Roland-Scholz/Sally-2/pictures/sally-2-abbuc-b.jpg

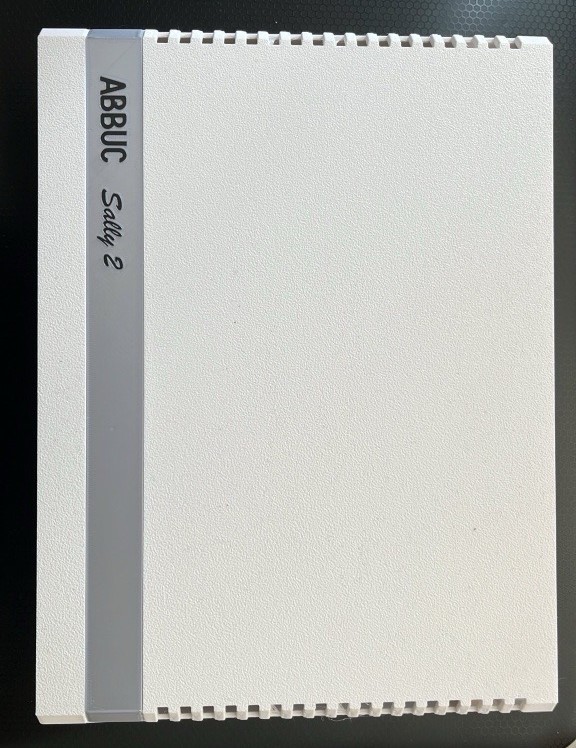
pictures/sally-2-abbuc-b.jpg
