Roland-Scholz/Sally-2/release/case/spacer-led.stl

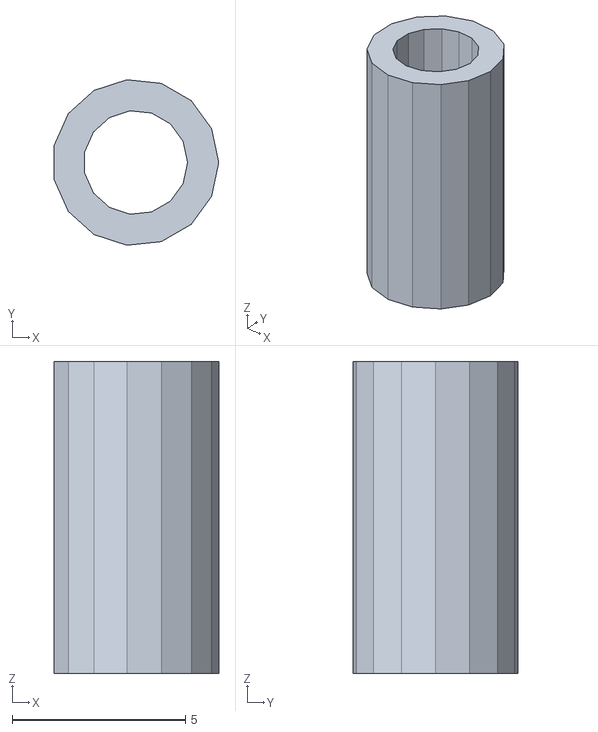
[picture p33: CAD file, 2025-09-01]
release/case/spacer-led.stl
4.75 x 4.77 x 9.00
