Roland-Scholz/Sally-2/case/sally-2-top-1a.stl

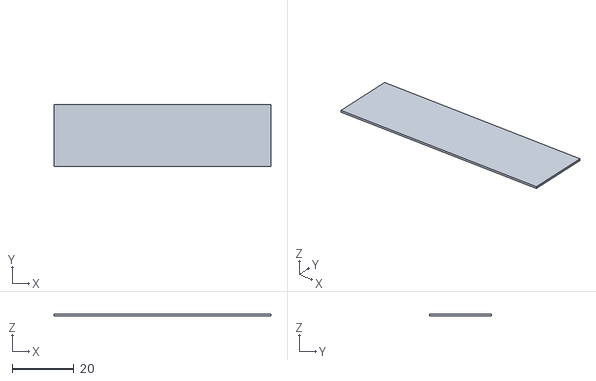
[picture p34: CAD file, 2025-05-10]
case/sally-2-top-1a.stl
70.0 x 20.0 x 0.6
