Roland-Scholz/Sally-2/release/case/sally-parts.3mf

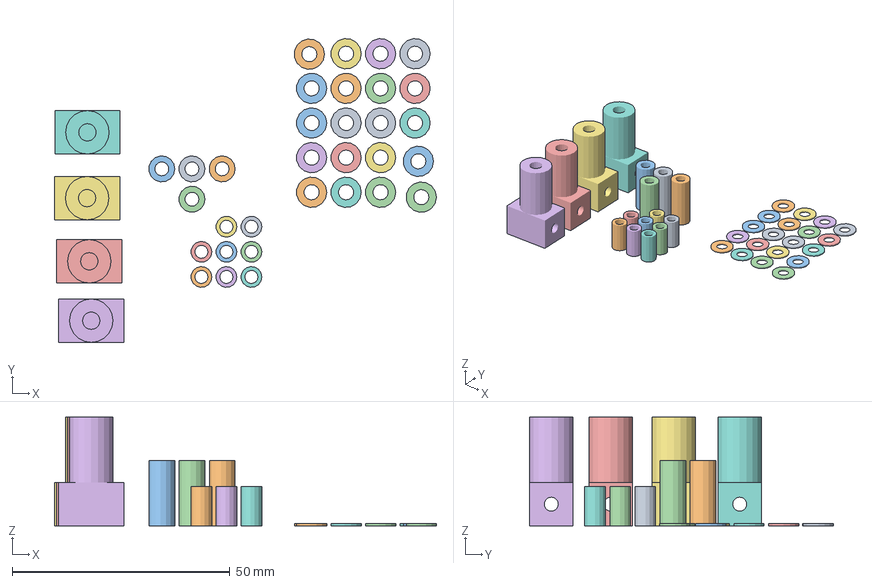
[picture p35: CAD file, 2025-09-01]
release/case/sally-parts.3mf
87.8 x 69.8 x 25.0 mm
spacer-round.stl x 4
washer.stl x 20
spacer.stl x 4
spacer-led.stl x 8
