Roland-Scholz/Sally-2/release/case/spacer.stl

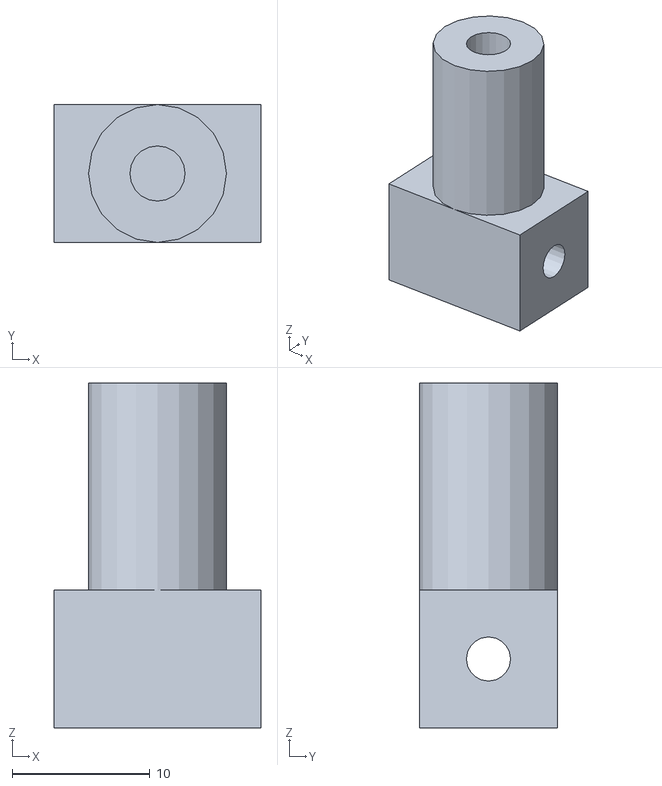
[picture p36: CAD file, 2025-09-01]
release/case/spacer.stl
15.0 x 10.0 x 25.0
