Roland-Scholz/Sally-2/case/spacer-led.scad

$fn = 15;

spacer_led();


module spacer_led() {
    difference(){
        cylinder(h=9, r=2.4);
            cylinder(h=9, r=1.5);
        
    };
}
