Roland-Scholz/Sally-2/case/spacer-round-15.scad

$fn = 15;

spacer_round_15();


module spacer_round_15() {
    difference(){
        cylinder(h=15, r=3);
            cylinder(h=15, r=1.6);
        
    };
}
