Roland-Scholz/Sally-2/case/spacer-round-9.scad

$fn = 15;

spacer_round_9();


module spacer_round_9() {
    difference(){
        cylinder(h=9, r=3);
            cylinder(h=9, r=1.6);
        
    };
}
