Roland-Scholz/Sally-2/LTspice/serout.asc

Q1: npn; BC547B
Q2: npn; BC547B
R1: res; 100000
R2: res; 1000
R3: res; 22000
R4: res; 47000
V1: voltage; EXP(0 5 0 0.000001 0.000052 0.0000001)
V2: voltage; 5
Named nets: output, 0, serin
.tran 0 0.0001 0
