Roland-Scholz/Sally-2/src/ddsysgen.asm

; Disassembly of the file "C:\github\Sally-1\ATR8000-CPM\ddsysgen.com"
; 
; CPU Type: Z80
; 
; Created with dZ80 2.0
; 
; on Monday, 26 of August 2024 at 07:51 PM
; 
0000 c30401    jp      0104h
0003 d431c1    call    nc,0c131h
0006 0d        dec     c
0007 2a0600    ld      hl,(0006h)
000a 01e0be    ld      bc,0bee0h
000d b7        or      a
000e ed42      sbc     hl,bc
0010 da0000    jp      c,0000h
0013 cd560a    call    0a56h
0016 0d        dec     c
0017 0a        ld      a,(bc)
0018 0a        ld      a,(bc)
0019 41        ld      b,c
001a 54        ld      d,h
001b 52        ld      d,d
001c 3830      jr      c,004eh          ; (+30h)
001e 3030      jr      nc,0050h         ; (+30h)
0020 2053      jr      nz,0075h         ; (+53h)
0022 79        ld      a,c
0023 73        ld      (hl),e
0024 74        ld      (hl),h
0025 65        ld      h,l
0026 6d        ld      l,l
0027 2047      jr      nz,0070h         ; (+47h)
0029 65        ld      h,l
002a 6e        ld      l,(hl)
002b 65        ld      h,l
002c 72        ld      (hl),d
002d 61        ld      h,c
002e 74        ld      (hl),h
002f 6f        ld      l,a
0030 72        ld      (hl),d
0031 2076      jr      nz,00a9h         ; (+76h)
0033 65        ld      h,l
0034 72        ld      (hl),d
0035 73        ld      (hl),e
0036 2032      jr      nz,006ah         ; (+32h)
0038 2e31      ld      l,31h
003a 0d        dec     c
003b 0a        ld      a,(bc)
003c 2d        dec     l
003d 2d        dec     l
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
00f4 69        ld      l,c
00f5 73        ld      (hl),e
00f6 6b        ld      l,e
00f7 2074      jr      nz,016dh         ; (+74h)
00f9 68        ld      l,b
00fa 61        ld      h,c
00fb 74        ld      (hl),h
00fc 2079      jr      nz,0177h         ; (+79h)
00fe 6f        ld      l,a
00ff 75        ld      (hl),l
0100 2077      jr      nz,0179h         ; (+77h)
0102 69        ld      l,c
0103 73        ld      (hl),e
0104 68        ld      l,b
0105 0d        dec     c
0106 0a        ld      a,(bc)
0107 74        ld      (hl),h
0108 6f        ld      l,a
0109 2077      jr      nz,0182h         ; (+77h)
010b 72        ld      (hl),d
010c 69        ld      l,c
010d 74        ld      (hl),h
010e 65        ld      h,l
010f 2043      jr      nz,0154h         ; (+43h)
0111 50        ld      d,b
0112 2f        cpl     
0113 4d        ld      c,l
0114 206f      jr      nz,0185h         ; (+6fh)
0116 6e        ld      l,(hl)
0117 74        ld      (hl),h
0118 6f        ld      l,a
0119 2069      jr      nz,0184h         ; (+69h)
011b 6e        ld      l,(hl)
011c 2064      jr      nz,0182h         ; (+64h)
011e 72        ld      (hl),d
011f 69        ld      l,c
0120 76        halt    
0121 65        ld      h,l
0122 2041      jr      nz,0165h         ; (+41h)
0124 3a2061    ld      a,(6120h)
0127 6e        ld      l,(hl)
0128 64        ld      h,h
0129 0d        dec     c
012a 0a        ld      a,(bc)
012b 00        nop     
012c af        xor     a
012d 323f0d    ld      (0d3fh),a
0130 3e02      ld      a,02h
0132 cd180b    call    0b18h
0135 20f9      jr      nz,0130h         ; (-07h)
0137 213d02    ld      hl,023dh
013a 220100    ld      (0001h),hl
013d 31c10d    ld      sp,0dc1h
0140 cd560a    call    0a56h
0143 0d        dec     c
0144 0a        ld      a,(bc)
0145 0a        ld      a,(bc)
0146 73        ld      (hl),e
0147 79        ld      a,c
0148 73        ld      (hl),e
0149 74        ld      (hl),h
014a 65        ld      h,l
014b 6d        ld      l,l
014c 2077      jr      nz,01c5h         ; (+77h)
014e 72        ld      (hl),d
014f 69        ld      l,c
0150 74        ld      (hl),h
0151 74        ld      (hl),h
0152 65        ld      h,l
0153 6e        ld      l,(hl)
0154 2061      jr      nz,01b7h         ; (+61h)
0156 6e        ld      l,(hl)
0157 64        ld      h,h
0158 2076      jr      nz,01d0h         ; (+76h)
015a 65        ld      h,l
015b 72        ld      (hl),d
015c 69        ld      l,c
015d 66        ld      h,(hl)
015e 69        ld      l,c
015f 65        ld      h,l
0160 64        ld      h,h
0161 206f      jr      nz,01d2h         ; (+6fh)
0163 6b        ld      l,e
0164 2e0d      ld      l,0dh
0166 0a        ld      a,(bc)
0167 70        ld      (hl),b
0168 72        ld      (hl),d
0169 65        ld      h,l
016a 73        ld      (hl),e
016b 73        ld      (hl),e
016c 2061      jr      nz,01cfh         ; (+61h)
016e 6e        ld      l,(hl)
016f 79        ld      a,c
0170 206b      jr      nz,01ddh         ; (+6bh)
0172 65        ld      h,l
0173 79        ld      a,c
0174 2074      jr      nz,01eah         ; (+74h)
0176 6f        ld      l,a
0177 2072      jr      nz,01ebh         ; (+72h)
0179 65        ld      h,l
017a 70        ld      (hl),b
017b 65        ld      h,l
017c 61        ld      h,c
017d 74        ld      (hl),h
017e 2061      jr      nz,01e1h         ; (+61h)
0180 67        ld      h,a
0181 61        ld      h,c
0182 69        ld      l,c
0183 6e        ld      l,(hl)
0184 206f      jr      nz,01f5h         ; (+6fh)
0186 72        ld      (hl),d
0187 0d        dec     c
0188 0a        ld      a,(bc)
0189 72        ld      (hl),d
018a 65        ld      h,l
018b 73        ld      (hl),e
018c 65        ld      h,l
018d 74        ld      (hl),h
018e 2074      jr      nz,0204h         ; (+74h)
0190 68        ld      l,b
0191 65        ld      h,l
0192 2041      jr      nz,01d5h         ; (+41h)
0194 54        ld      d,h
0195 52        ld      d,d
0196 3830      jr      c,01c8h          ; (+30h)
0198 3030      jr      nc,01cah         ; (+30h)
019a 2061      jr      nz,01fdh         ; (+61h)
019c 6e        ld      l,(hl)
019d 64        ld      h,h
019e 2072      jr      nz,0212h         ; (+72h)
01a0 65        ld      h,l
01a1 2d        dec     l
01a2 62        ld      h,d
01a3 6f        ld      l,a
01a4 6f        ld      l,a
01a5 74        ld      (hl),h
01a6 0d        dec     c
01a7 0a        ld      a,(bc)
01a8 43        ld      b,e
01a9 50        ld      d,b
01aa 2f        cpl     
01ab 4d        ld      c,l
01ac 202e      jr      nz,01dch         ; (+2eh)
01ae 2e2e      ld      l,2eh
01b0 2000      jr      nz,01b2h         ; (+00h)
01b2 cdeb09    call    09ebh
01b5 cd560a    call    0a56h
01b8 0d        dec     c
01b9 0a        ld      a,(bc)
01ba 00        nop     
01bb c33002    jp      0230h
01be 04        inc     b
01bf 2030      jr      nz,01f1h         ; (+30h)
01c1 cd560a    call    0a56h
01c4 0d        dec     c
01c5 0a        ld      a,(bc)
01c6 2020      jr      nz,01e8h         ; (+20h)
01c8 2066      jr      nz,0230h         ; (+66h)
01ca 75        ld      (hl),l
01cb 6e        ld      l,(hl)
01cc 63        ld      h,e
01cd 74        ld      (hl),h
01ce 69        ld      l,c
01cf 6f        ld      l,a
01d0 6e        ld      l,(hl)
01d1 73        ld      (hl),e
01d2 2061      jr      nz,0235h         ; (+61h)
01d4 76        halt    
01d5 61        ld      h,c
01d6 69        ld      l,c
01d7 6c        ld      l,h
01d8 61        ld      h,c
01d9 62        ld      h,d
01da 6c        ld      l,h
01db 65        ld      h,l
01dc 3a0d0a    ld      a,(0a0dh)
01df 0a        ld      a,(bc)
01e0 312920    ld      sp,2029h
01e3 52        ld      d,d
01e4 65        ld      h,l
01e5 61        ld      h,c
01e6 64        ld      h,h
01e7 2073      jr      nz,025ch         ; (+73h)
01e9 79        ld      a,c
01ea 73        ld      (hl),e
01eb 74        ld      (hl),h
01ec 65        ld      h,l
01ed 6d        ld      l,l
01ee 2074      jr      nz,0264h         ; (+74h)
01f0 72        ld      (hl),d
01f1 61        ld      h,c
01f2 63        ld      h,e
01f3 6b        ld      l,e
01f4 73        ld      (hl),e
01f5 2066      jr      nz,025dh         ; (+66h)
01f7 72        ld      (hl),d
01f8 6f        ld      l,a
01f9 6d        ld      l,l
01fa 2064      jr      nz,0260h         ; (+64h)
01fc 69        ld      l,c
01fd 73        ld      (hl),e
01fe 6b        ld      l,e
01ff 2e0d      ld      l,0dh
0201 0a        ld      a,(bc)
0202 322920    ld      (2029h),a
0205 57        ld      d,a
0206 72        ld      (hl),d
0207 69        ld      l,c
0208 74        ld      (hl),h
0209 65        ld      h,l
020a 2073      jr      nz,027fh         ; (+73h)
020c 79        ld      a,c
020d 73        ld      (hl),e
020e 74        ld      (hl),h
020f 65        ld      h,l
0210 6d        ld      l,l
0211 2074      jr      nz,0287h         ; (+74h)
0213 72        ld      (hl),d
0214 61        ld      h,c
0215 63        ld      h,e
0216 6b        ld      l,e
0217 73        ld      (hl),e
0218 2074      jr      nz,028eh         ; (+74h)
021a 6f        ld      l,a
021b 2064      jr      nz,0281h         ; (+64h)
021d 69        ld      l,c
021e 73        ld      (hl),e
021f 6b        ld      l,e
0220 2e0d      ld      l,0dh
0222 0a        ld      a,(bc)
0223 33        inc     sp
0224 29        add     hl,hl
0225 2047      jr      nz,026eh         ; (+47h)
0227 65        ld      h,l
0228 6e        ld      l,(hl)
0229 65        ld      h,l
022a 72        ld      (hl),d
022b 61        ld      h,c
022c 74        ld      (hl),h
022d 65        ld      h,l
022e 2063      jr      nz,0293h         ; (+63h)
0230 75        ld      (hl),l
0231 73        ld      (hl),e
0232 74        ld      (hl),h
0233 6f        ld      l,a
0234 6d        ld      l,l
0235 69        ld      l,c
0236 7a        ld      a,d
0237 65        ld      h,l
0238 64        ld      h,h
0239 2043      jr      nz,027eh         ; (+43h)
023b 50        ld      d,b
023c 2f        cpl     
023d 4d        ld      c,l
023e 200d      jr      nz,024dh         ; (+0dh)
0240 0a        ld      a,(bc)
0241 00        nop     
0242 cd560a    call    0a56h
0245 0d        dec     c
0246 0a        ld      a,(bc)
0247 65        ld      h,l
0248 6e        ld      l,(hl)
0249 74        ld      (hl),h
024a 65        ld      h,l
024b 72        ld      (hl),d
024c 206e      jr      nz,02bch         ; (+6eh)
024e 75        ld      (hl),l
024f 6d        ld      l,l
0250 62        ld      h,d
0251 65        ld      h,l
0252 72        ld      (hl),d
0253 206f      jr      nz,02c4h         ; (+6fh)
0255 66        ld      h,(hl)
0256 2066      jr      nz,02beh         ; (+66h)
0258 75        ld      (hl),l
0259 6e        ld      l,(hl)
025a 63        ld      h,e
025b 74        ld      (hl),h
025c 69        ld      l,c
025d 6f        ld      l,a
025e 6e        ld      l,(hl)
025f 2028      jr      nz,0289h         ; (+28h)
0261 312c32    ld      sp,322ch
0264 206f      jr      nz,02d5h         ; (+6fh)
0266 72        ld      (hl),d
0267 2033      jr      nz,029ch         ; (+33h)
0269 29        add     hl,hl
026a 200d      jr      nz,0279h         ; (+0dh)
026c 0a        ld      a,(bc)
026d 6f        ld      l,a
026e 72        ld      (hl),d
026f 2070      jr      nz,02e1h         ; (+70h)
0271 72        ld      (hl),d
0272 65        ld      h,l
0273 73        ld      (hl),e
0274 73        ld      (hl),e
0275 203c      jr      nz,02b3h         ; (+3ch)
0277 43        ld      b,e
0278 54        ld      d,h
0279 4c        ld      c,h
027a 2d        dec     l
027b 43        ld      b,e
027c 3e20      ld      a,20h
027e 74        ld      (hl),h
027f 6f        ld      l,a
0280 2065      jr      nz,02e7h         ; (+65h)
0282 78        ld      a,b
0283 69        ld      l,c
0284 74        ld      (hl),h
0285 2074      jr      nz,02fbh         ; (+74h)
0287 6f        ld      l,a
0288 2043      jr      nz,02cdh         ; (+43h)
028a 50        ld      d,b
028b 2f        cpl     
028c 4d        ld      c,l
028d 202e      jr      nz,02bdh         ; (+2eh)
028f 2e2e      ld      l,2eh
0291 2000      jr      nz,0293h         ; (+00h)
0293 cd0b0a    call    0a0bh
0296 fe31      cp      31h
0298 2006      jr      nz,02a0h         ; (+06h)
029a cdcd0a    call    0acdh
029d c3dd03    jp      03ddh
02a0 fe32      cp      32h
02a2 2006      jr      nz,02aah         ; (+06h)
02a4 cd7e0a    call    0a7eh
02a7 c3dd03    jp      03ddh
02aa fe33      cp      33h
02ac c2b503    jp      nz,03b5h
02af cd6e04    call    046eh
02b2 c3dd03    jp      03ddh
02b5 fe58      cp      58h
02b7 ca340a    jp      z,0a34h
02ba cd560a    call    0a56h
02bd 0d        dec     c
02be 0a        ld      a,(bc)
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
0d6f c9        ret     

0d70 110050    ld      de,5000h
0d73 212a0e    ld      hl,0e2ah
0d76 46        ld      b,(hl)
0d77 23        inc     hl
0d78 cd1f0e    call    0e1fh
0d7b 10fb      djnz    0d78h            ; (-05h)
0d7d 0e09      ld      c,09h
0d7f 210000    ld      hl,0000h
