Roland-Scholz/Sally-2/src/bootsec.asm

                    ld      sp,$0080                        ;[0080] 31 80 00
                    ld      ix,$00f3                        ;[0083] dd 21 f3 00
                    ld      b,$0e                           ;[0087] 06 0e
                    push    bc                              ;[0089] c5
                    call    $f00f                           ;[008a] cd 0f f0
                    pop     bc                              ;[008d] c1
                    ld      a,($00fb)                       ;[008e] 3a fb 00
                    or      a                               ;[0091] b7
                    jr      nz,$00ba                        ;[0092] 20 26
                    ld      a,($00f6)                       ;[0094] 3a f6 00
                    inc     a                               ;[0097] 3c
                    cp      $0b                             ;[0098] fe 0b
                    jr      c,$00a1                         ;[009a] 38 05
                    ld      a,$01                           ;[009c] 3e 01
                    ld      ($00f5),a                       ;[009e] 32 f5 00
                    ld      ($00f6),a                       ;[00a1] 32 f6 00
                    ld      hl,$00f8                        ;[00a4] 21 f8 00
                    inc     (hl)                            ;[00a7] 34
                    inc     (hl)                            ;[00a8] 34
                    djnz    $0089                           ;[00a9] 10 de
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
                    call    nc,$0200                        ;[00f8] d4 00 02
                    nop                                     ;[00fb] 00
                    call    $0000                           ;[00fc] cd 00 00
                    nop                                     ;[00ff] 00
