Roland-Scholz/Sally-2/pictures/Sally-2-top.jpeg

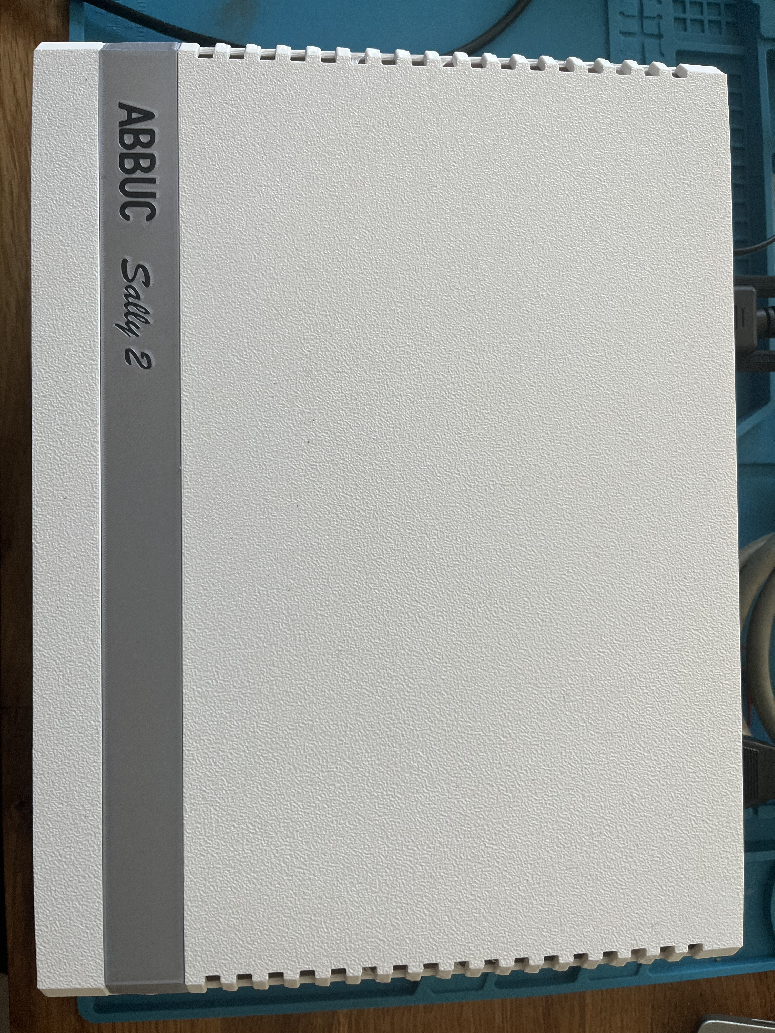
pictures/Sally-2-top.jpeg
